drfailov/DRM_Watch_v2/Photos/2022-01-16 DRMW2_DOC.png

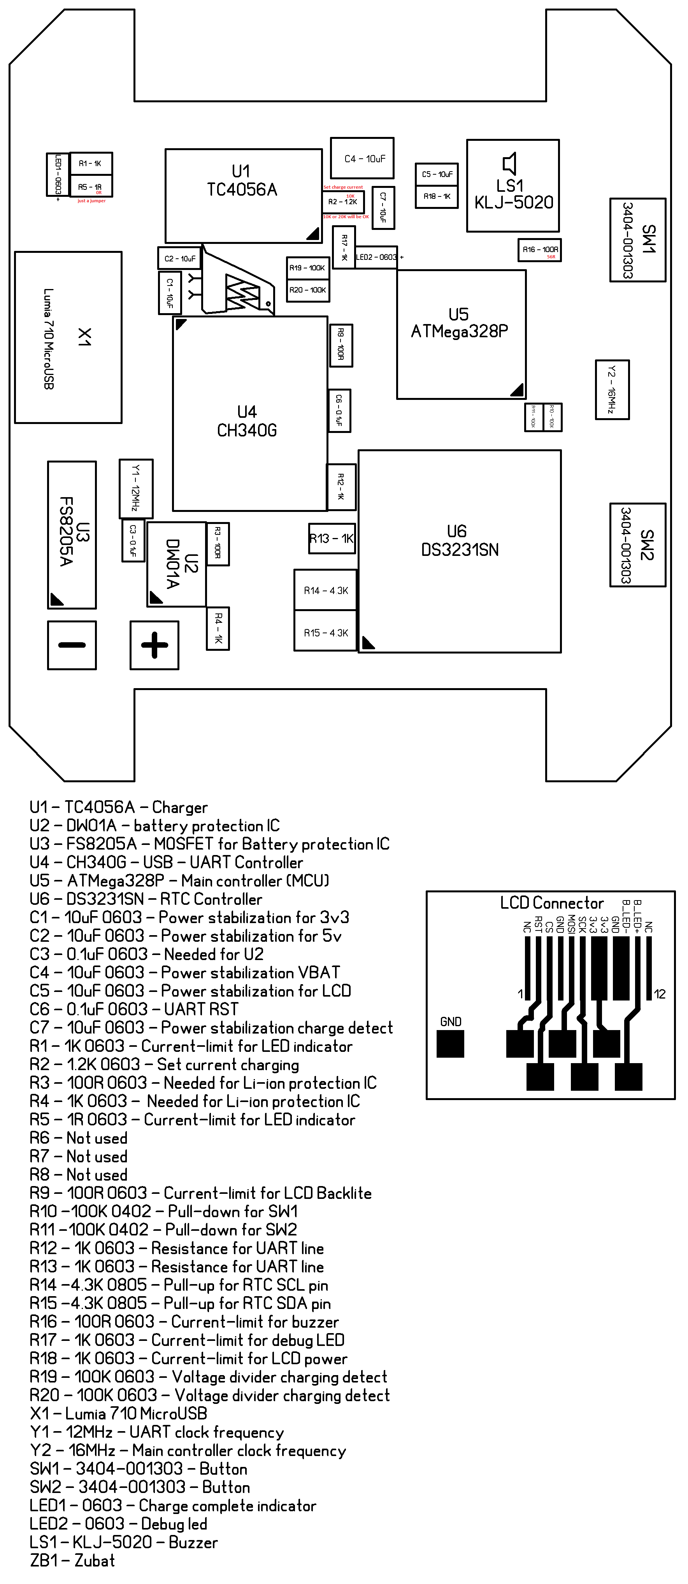
Photos/2022-01-16 DRMW2_DOC.png
