drfailov/DRM_Watch_v2/Photos/2022-03-02 Promo for repository DRM Watch.jpg

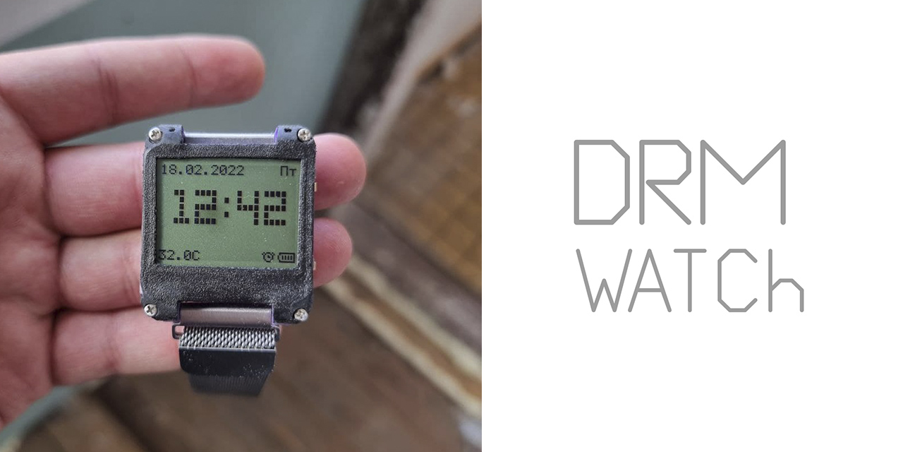
Photos/2022-03-02 Promo for repository DRM Watch.jpg
