drfailov/DRM_Watch_v2/Photos/20220228_160352.jpg

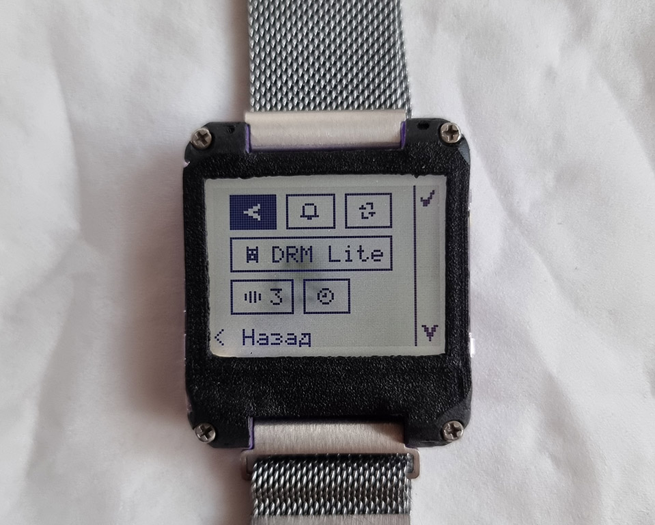
Photos/20220228_160352.jpg
