drfailov/DRM_Watch_v2/Photos/config_watchfaces.jpg

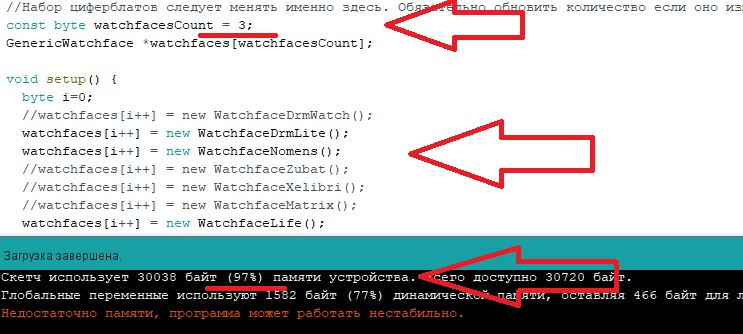
Photos/config_watchfaces.jpg
