drfailov/DRM_Watch_v2/Photos/DRMWatch.png

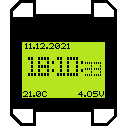
Photos/DRMWatch.png
