drfailov/DRM_Watch_v2/Photos/photo_2021-10-14_18-44-58.jpg

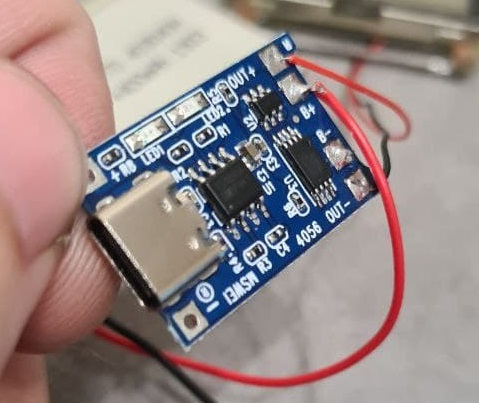
Photos/photo_2021-10-14_18-44-58.jpg
