drfailov/DRM_Watch_v2/Photos/photo_2021-10-16_11-53-57.jpg

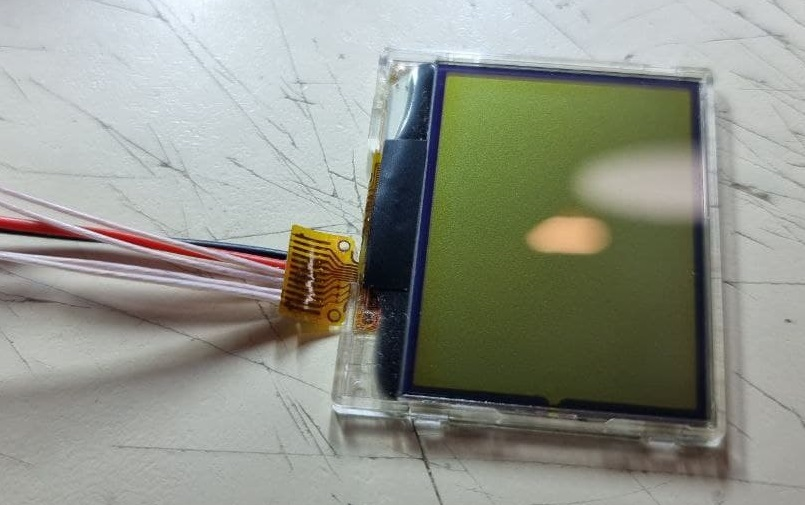
Photos/photo_2021-10-16_11-53-57.jpg
