drfailov/DRM_Watch_v2/Photos/photo_2021-11-30_09-08-52.jpg

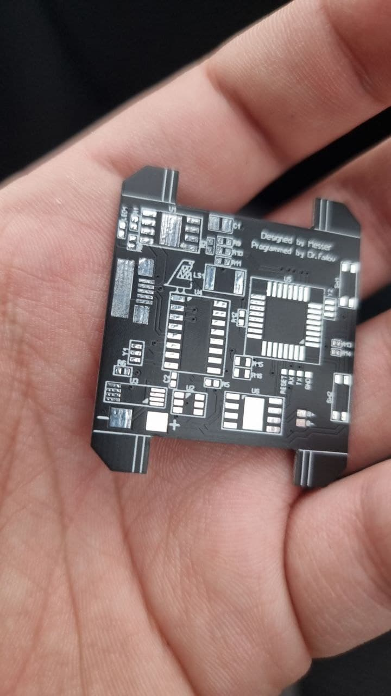
Photos/photo_2021-11-30_09-08-52.jpg
