drfailov/DRM_Watch_v2/Photos/photo_2021-12-01_08-44-34.jpg

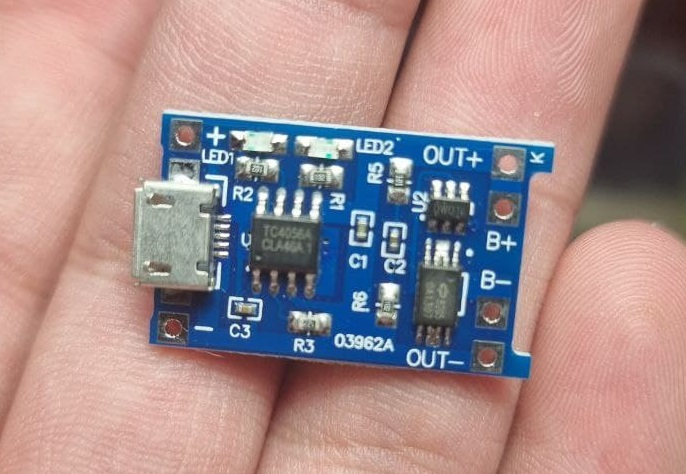
Photos/photo_2021-12-01_08-44-34.jpg
