drfailov/DRM_Watch_v2/Photos/photo_2021-12-01_15-29-12.jpg

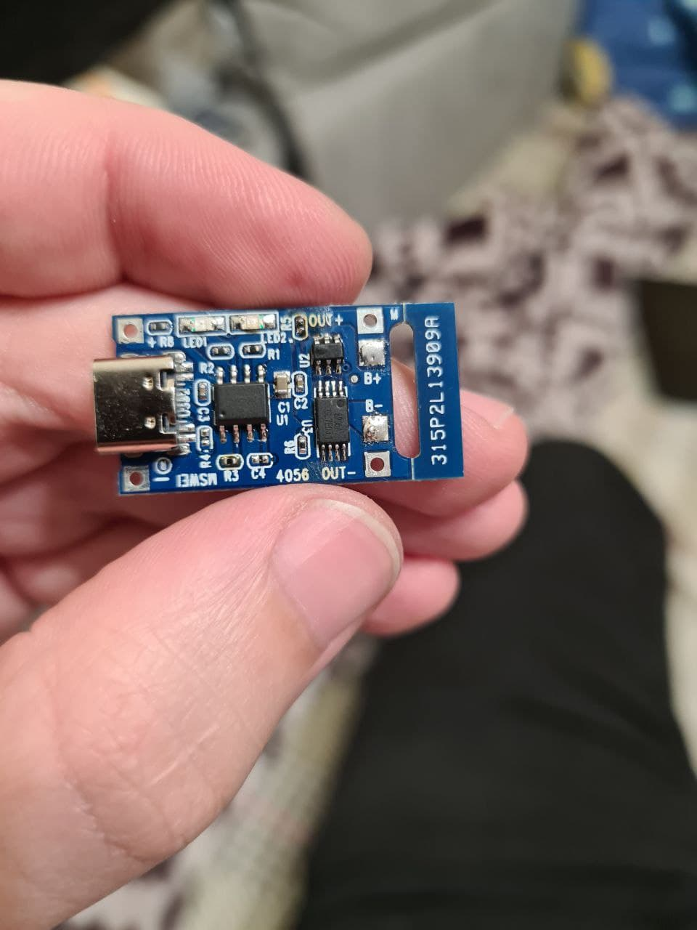
Photos/photo_2021-12-01_15-29-12.jpg
