drfailov/DRM_Watch_v2/Photos/photo_2021-12-19_19-43-52 (4).jpg

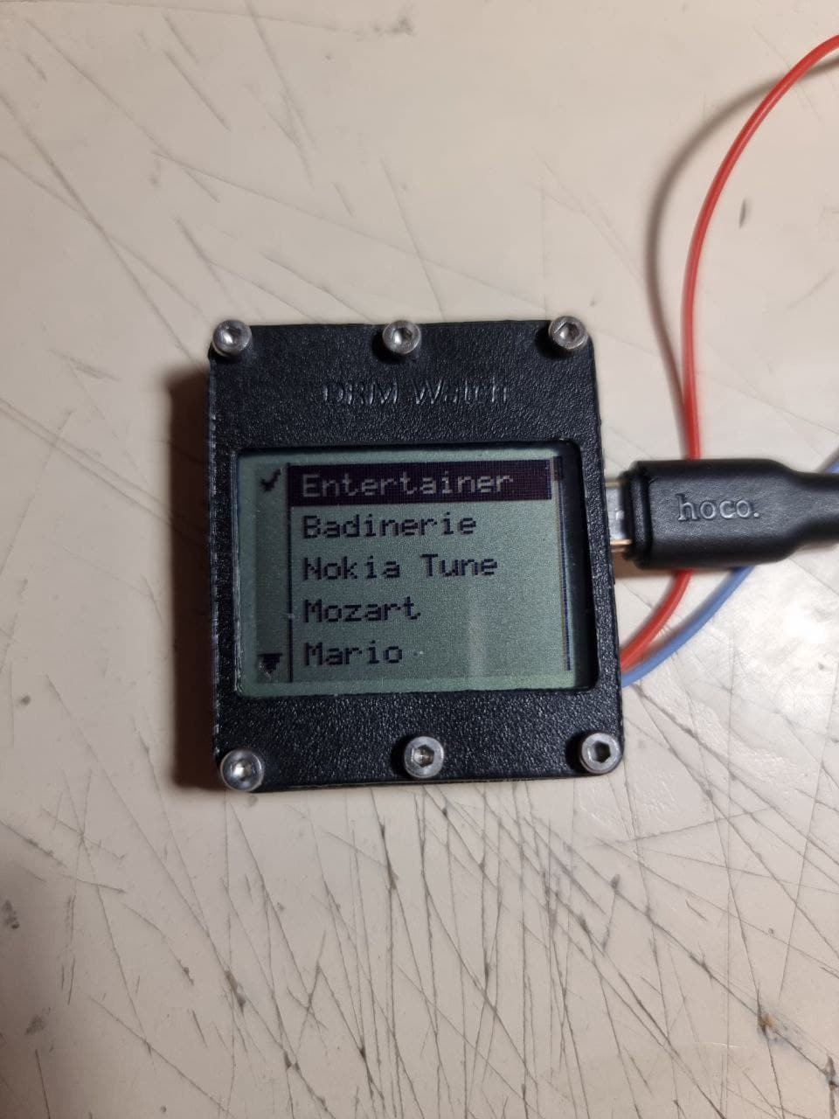
Photos/photo_2021-12-19_19-43-52 (4).jpg
