drfailov/DRM_Watch_v2/Photos/photo_2021-12-31_22-29-40.jpg

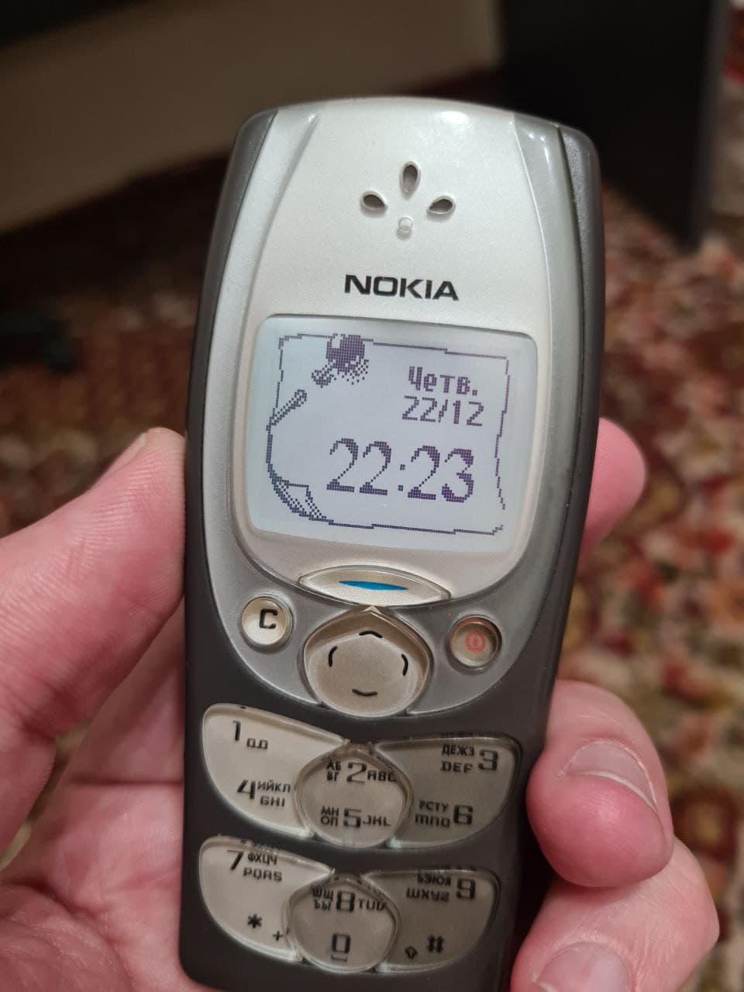
Photos/photo_2021-12-31_22-29-40.jpg
