drfailov/DRM_Watch_v2/Photos/photo_2022-01-07_13-40-24.jpg

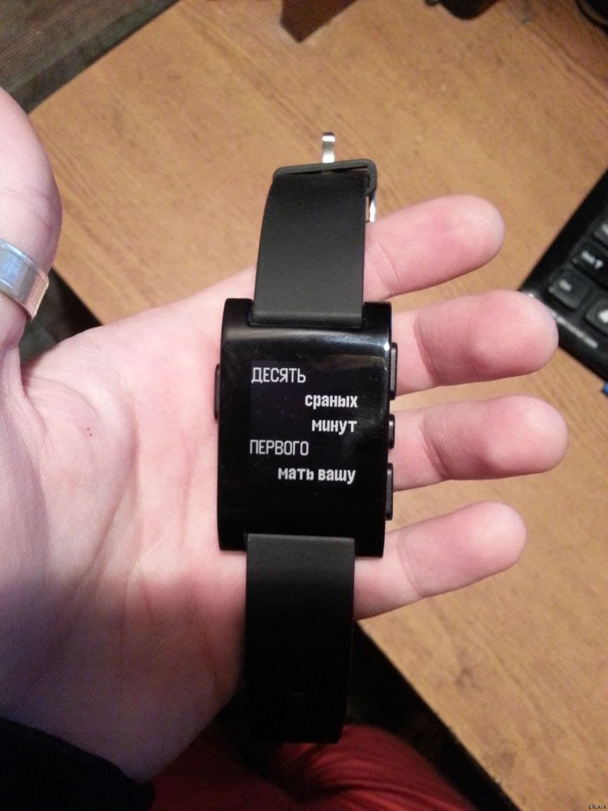
Photos/photo_2022-01-07_13-40-24.jpg
