drfailov/DRM_Watch_v2/Photos/photo_2022-03-16_15-22-59.jpg

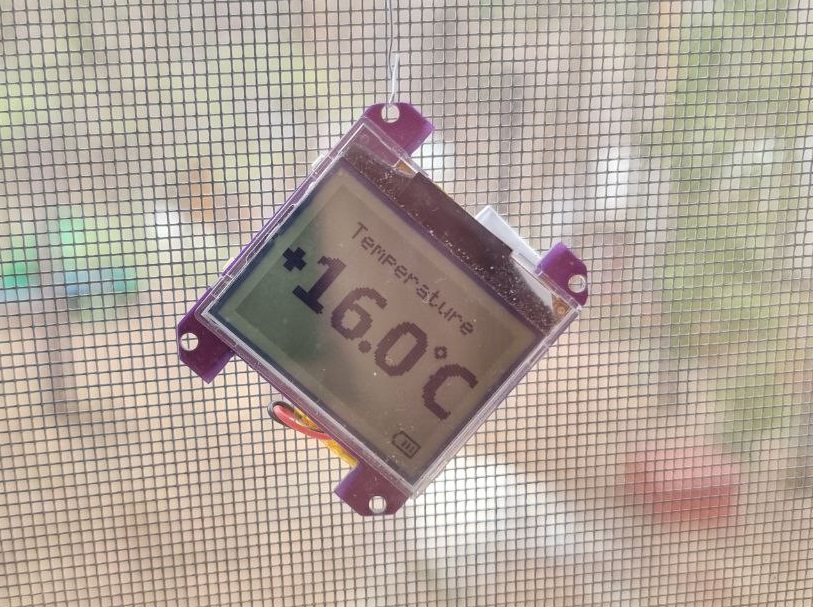
Photos/photo_2022-03-16_15-22-59.jpg
