drfailov/DRM_Watch_v2/Photos/photo_2023-04-07_19-43-56.jpg

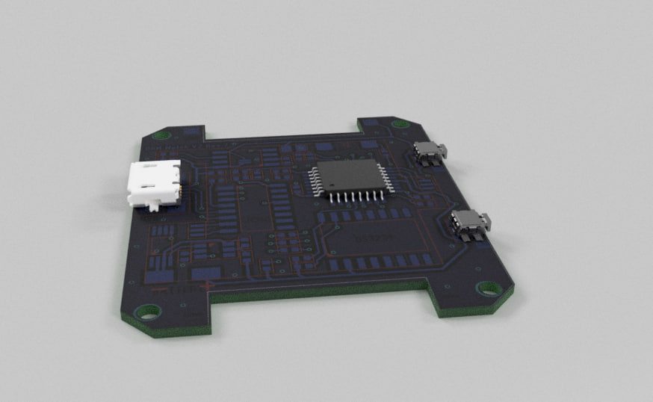
Photos/photo_2023-04-07_19-43-56.jpg
