drfailov/DRM_Watch_v2/Photos/photo_2023-04-19_00-23-33.jpg

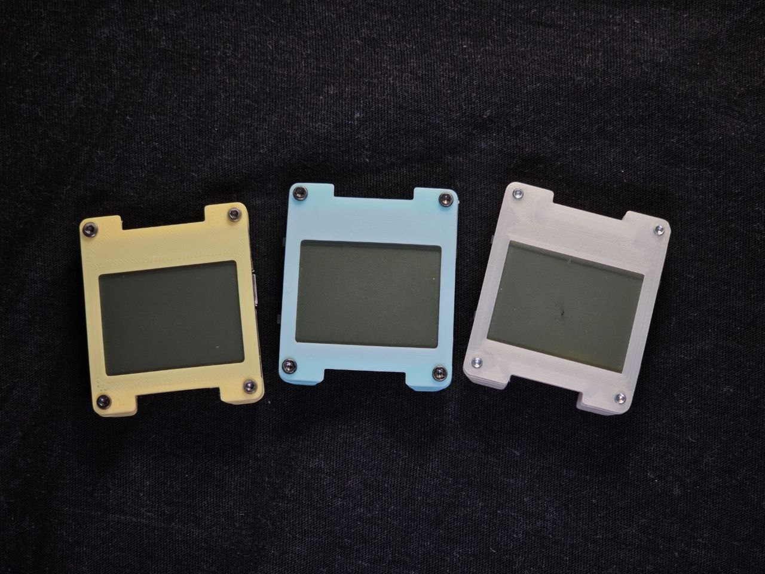
Photos/photo_2023-04-19_00-23-33.jpg
