drfailov/DRM_Watch_v2/Photos/Screenshot 2023-04-07 202631.jpg

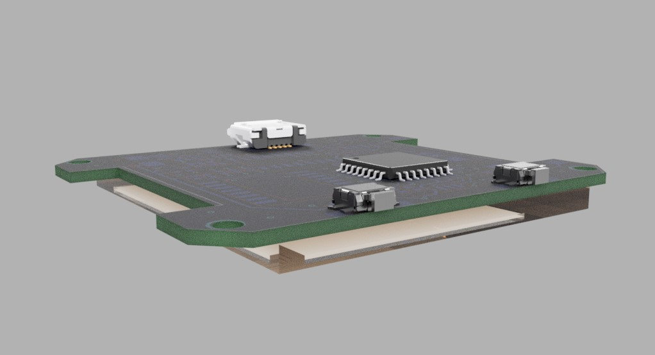
Photos/Screenshot 2023-04-07 202631.jpg
