drfailov/DRM_Watch_v2/Photos/Screenshot 2023-04-07 212515.jpg

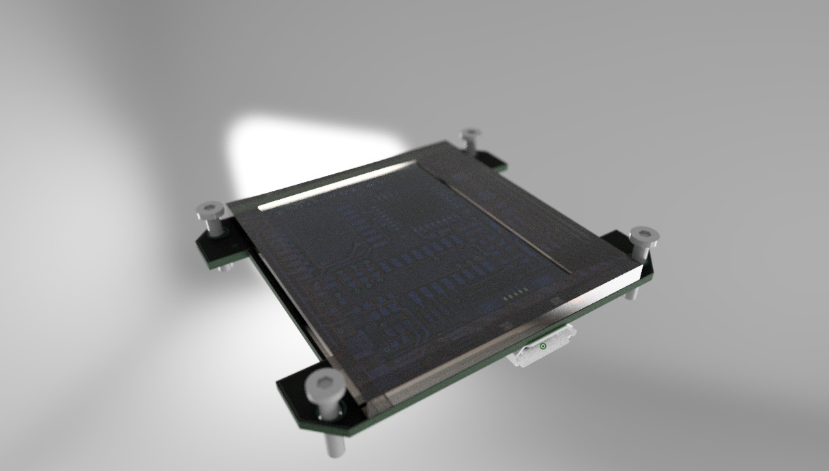
Photos/Screenshot 2023-04-07 212515.jpg
