drfailov/DRM_Watch_v2/Photos/Screenshot 2023-04-07 212542.jpg

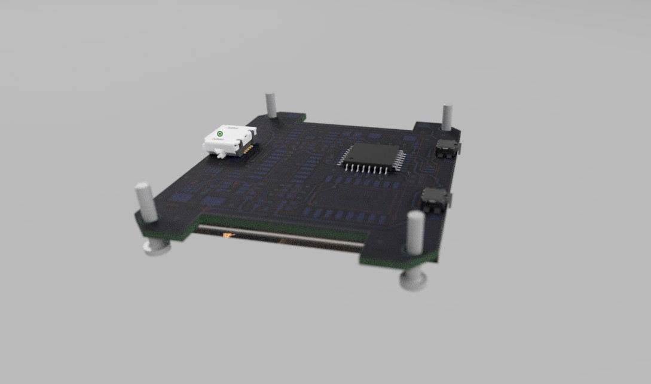
Photos/Screenshot 2023-04-07 212542.jpg
