drfailov/DRM_Watch_v2/Photos/v4 20mm.JPG

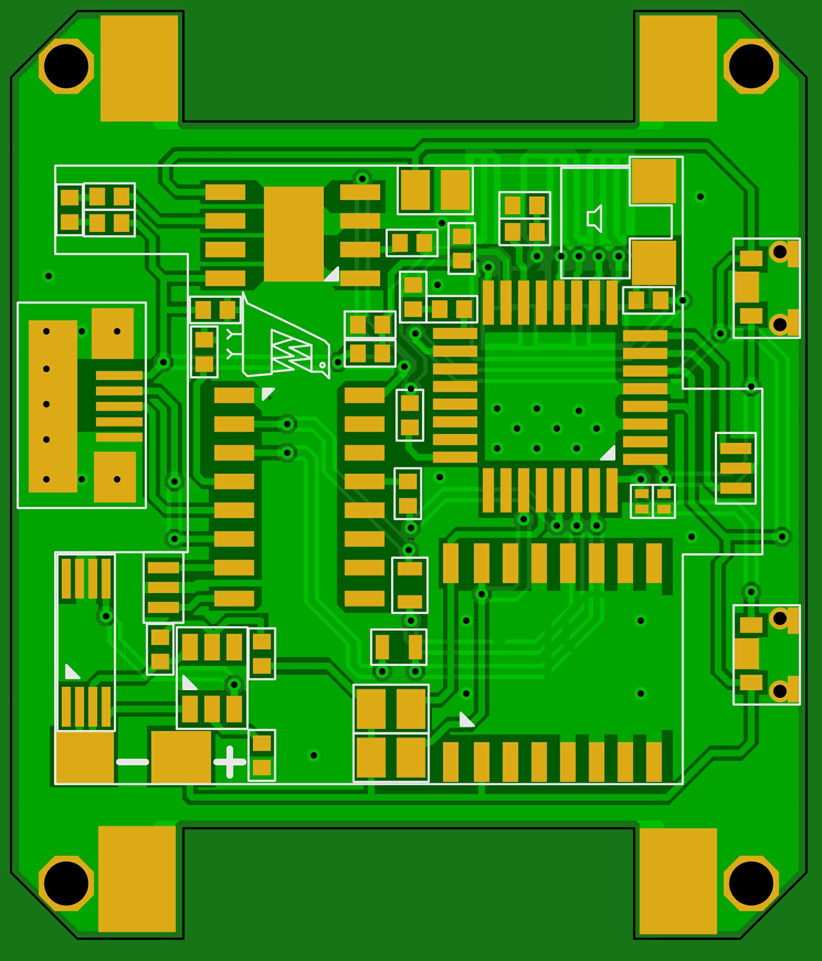
Photos/v4 20mm.JPG
