drfailov/DRM_Watch_v2/Case/Back Case v8.step

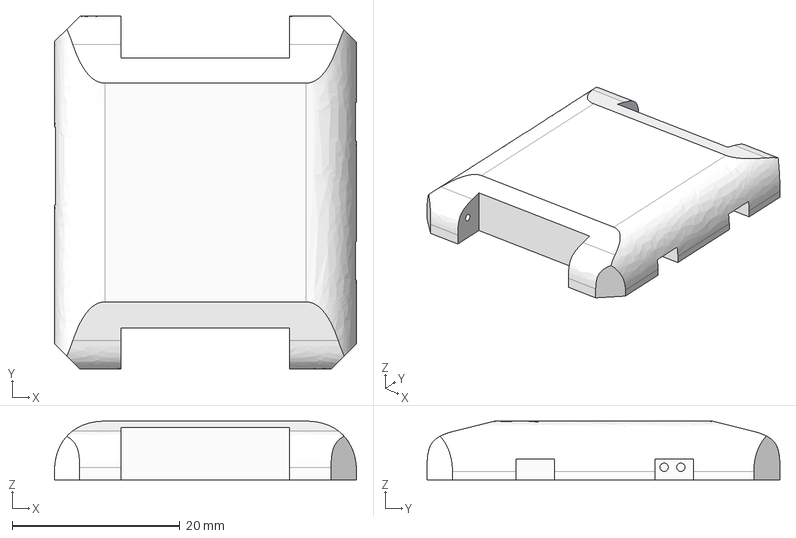
[picture p144: CAD file, 2022-01-25]
Case/Back Case v8.step
36.0 x 42.1 x 7.00 mm
