drfailov/DRM_Watch_v2/Arduino Program/_DRMWatch2/MelodyPlayer.ino

const byte groovyBlue[] PROGMEM = {
  125,
  0b10011101, 0b00100100, 0b00100100, 0b00100100, 0b00100100,
  0b10011000, 0b10011011, 0b10011000, 0b10011011, 0b10011101,
  0b00100100, 0b00100100, 0b00100100, 0b00100100, 0b10011000,
  0b10011011, 0b10011000, 0b10011011, 0b01011101, 0b10010001,
  0b01100100, 0b10010001, 0b01100100, 0b10010001, 0b01100100,
  0b10010001, 0b01100100, 0b10010001, 0b01100100, 0b10010001,
  0b01100100, 0b10011000, 0b10011011, 0b10011000, 0b10011011,
  0b01011101, 0b10011101, 0b01100100, 0b10011101, 0b01100100,
  0b10011101, 0b01100100, 0b10011101, 0b01100100, 0b10011101,
  0b01100100, 0b10011101, 0b01100100, 0b10011000, 0b10011011,
  0b10011000, 0b10011011, 0b01011101, 0b10011101, 0b01100000,
  0b10011101, 0b01100010, 0b10011101, 0b01100100, 0b10011101,
  0b01100000, 0b10011101, 0b10100010, 0b10100100, 0b10011101,
  0b01100100, 0b10011000, 0b10011011, 0b10011000, 0b10011011,
  0b01011101, 0b10011101, 0b01100000, 0b10011101, 0b01100010,
  0b10011101, 0b01100100, 0b10011101, 0b01100000, 0b10011101,
  0b10100010, 0b10100100, 0b10011101, 0b01100100, 0b10011000,
  0b10011011, 0b10011000, 0b10011011, 0b01011101, 0b10011101,
  0b01100000, 0b10011101, 0b01100011, 0b10011101, 0b01100010,
  0b10011101, 0b01100001, 0b10011101, 0b01100000, 0b10011101,
  0b01011111, 0b00100100, 0b10011000, 0b10011011, 0b10011000,
  0b10011011, 0b01011101, 0b11111111,
};
const byte* const getMelodyGroovyBlue() {
  return groovyBlue;
}


const byte blue[] PROGMEM = {
    140,
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

const char* const modeMenuMelodiesItems[] PROGMEM = {
  menuItemBack,
  modeMenuMelodiesItem1,
  modeMenuMelodiesItem2,
  modeMenuMelodiesItem3,
  modeMenuMelodiesItem4,
  modeMenuMelodiesItem5,
  modeMenuMelodiesItem6,
  modeMenuMelodiesItem7,
  modeMenuMelodiesItem8,
  modeMenuMelodiesItem9
};

byte getMelodyCount(){ return 9;}
const char* getMelodyName(byte index){
  return pgm_read_word(&modeMenuMelodiesItems[index+1]);
}
const byte* const getMelodyByIndex(byte index){
  if (index == 0) 
    return getMelodyEntertainer();
  if (index == 1)  
    return getMelodyBadinerie();
  if (index == 2)  
    return getMelodyNokiaTune();
  if (index == 3) 
    return getMelodyMozart();
  if (index == 4) 
    return getMelodyMario();
  if (index == 5) 
    return getMelodyGroovyBlue();
  if (index == 6) 
    return getMelodyUkraine();
  if (index == 7) 
    return getMelodyBlue();  
  if (index == 8) 
    return getMelodyWasWollenWirTrinken();    
}







bool melodyPlayerLoopMelody = false;

//return true if was played completely or false if interrupted
bool melodyPlayerPlayMelody(const byte* const melody) {
  displayTransition();
  melodyPlayerLoopMelody = false;
  do{
    melodyPlayerDrawScreen();
    pinMode(pinBuzzer, OUTPUT);
    byte length = melodyPlayerGetLength(melody);
    float tempo = pgm_read_byte(&melody[0]);
    float whole_notes_per_second = tempo / 240.0;
    for (byte i = 1; i < length - 1; i++) {
      byte b = pgm_read_byte(&melody[i]);
      byte duration = 0;
      if (bitRead(b, 7) == 0 && bitRead(b, 6) == 0) duration = 4;
      if (bitRead(b, 7) == 0 && bitRead(b, 6) == 1) duration = 8;
      if (bitRead(b, 7) == 1 && bitRead(b, 6) == 0) duration = 16;
      if (bitRead(b, 7) == 1 && bitRead(b, 6) == 1) duration = 32;
      float timeMs = 1000.0 / (whole_notes_per_second * duration);
      byte noteNumberByte = 0;
      for (byte i = 0; i < 6; i++)
        bitWrite(noteNumberByte, i, bitRead(b, i));
      float noteNumber = noteNumberByte;
      // Note frequency is calculated as (F*2^(n/12)),
      // We can use C2=65.41, or C3=130.81. C2 is a bit shorter.
      float frequency = 0;
      //290 is ok
      if (noteNumber < 36)
        frequency = 250.0 * pow(2.0, (noteNumber / 12.0));
  
      if (frequency != 0){
        displayBacklightOn();
        tone(pinBuzzer, frequency);
      }
      else{
        noTone(pinBuzzer);
      }
      long noteStarted = millis();
      while(millis() - noteStarted < timeMs);
      noTone(pinBuzzer);
      displayBacklightOff();
      delay(13);
      
      if (isButtonUpPressed()){
        if(isButtonUpHold()){
          melodyPlayerLoopMelody = !melodyPlayerLoopMelody;
          melodyPlayerDrawScreen();
        }
        else{
          displayBacklightOn();
          return false;
        }
      }
    }
    
    noTone(pinBuzzer);
    //pinMode(pinBuzzer, INPUT);
    delay(1000);
  }while(melodyPlayerLoopMelody);
  displayBacklightOn();
  return true;
}

void melodyPlayerDrawScreen() {
  displayClear();
  displayDrawVector(/*path*/getPathZubat(), /*x*/24, /*y*/10, /*animate*/false, /*color*/1);
#ifdef LANG_EN
  displayDrawText(20, 60, 1, F("Playing..."));
#endif
#ifdef LANG_RU
  displayDrawText(17, 60, 1, F("Пoпиликaeм!"));
#endif
#ifdef LANG_UA
  displayDrawText(20, 60, 1, F("Виконую..."));
#endif

  if(!melodyPlayerLoopMelody){
    byte hour = rtcGetHours();
    byte minute = rtcGetMinutes();
    sprintf(buffer, timeFormat, hour, minute);
    displayDrawText(0, 0, 1, buffer);
  }
  else{
    displayDrawIconFlip(0, 0, 1);
  }
  
  displayDrawBattery(79, 0);
  displayUpdate();
}

void printBits(byte myByte) {
  for (byte mask = 0x80; mask; mask >>= 1) {
    if (mask & myByte)
      Serial.print('1');
    else
      Serial.print('0');
  }
}

int melodyPlayerGetLength(const byte* const melody) {
  for (byte i = 0; i < 254; i++) {
    byte b = pgm_read_byte(&melody[i]);
    if (b == 0b11111111) {
      return i + 1;
    }
  }
}
