drfailov/DRM_Watch_v2/Arduino Program/_DRMWatch2/WatchfaceThermo.ino

// 'calibri0', 17x23px
const unsigned char  thermo0 [] PROGMEM = {
  0x80, 0xf0, 0xfc, 0xfe, 0xfe, 0x3f, 0x0f, 0x0f, 0x0f, 0x0f, 0x0f, 0x1f, 0xff, 0xfe, 0xfc, 0xf8, 
  0xe0, 0xff, 0xff, 0xff, 0xff, 0xff, 0x00, 0x00, 0x00, 0x00, 0x00, 0x00, 0x00, 0xff, 0xff, 0xff, 
  0xff, 0xff, 0x01, 0x0f, 0x1f, 0x3f, 0x7f, 0x7e, 0x78, 0x70, 0x70, 0x70, 0x78, 0x7c, 0x7f, 0x3f, 
  0x1f, 0x0f, 0x01
};
// 'calibri1', 17x23px
const unsigned char  thermo1 [] PROGMEM = {
  0x00, 0x00, 0x78, 0x38, 0x3c, 0x1c, 0x1e, 0xff, 0xff, 0xff, 0xff, 0xff, 0x00, 0x00, 0x00, 0x00, 
  0x00, 0x00, 0x00, 0x00, 0x00, 0x00, 0x00, 0x00, 0xff, 0xff, 0xff, 0xff, 0xff, 0x00, 0x00, 0x00, 
  0x00, 0x00, 0x00, 0x00, 0x78, 0x78, 0x78, 0x78, 0x78, 0x7f, 0x7f, 0x7f, 0x7f, 0x7f, 0x78, 0x78, 
  0x78, 0x78, 0x20
};
// 'calibri2', 17x23px
const unsigned char  thermo2 [] PROGMEM = {
  0x00, 0x3c, 0x1e, 0x1e, 0x0f, 0x0f, 0x0f, 0x0f, 0x0f, 0x1f, 0xff, 0xff, 0xfe, 0xfe, 0xfc, 0xf0, 
  0x00, 0x00, 0x00, 0x00, 0x00, 0x80, 0xc0, 0xe0, 0xf0, 0xf8, 0xfe, 0x7f, 0x3f, 0x1f, 0x0f, 0x07, 
  0x00, 0x00, 0x00, 0x7c, 0x7e, 0x7f, 0x7f, 0x7f, 0x7f, 0x7b, 0x79, 0x78, 0x78, 0x78, 0x78, 0x78, 
  0x78, 0x78, 0x70
};
// 'calibri3', 17x23px
const unsigned char  thermo3 [] PROGMEM = {
  0x00, 0x1c, 0x1e, 0x0e, 0x0f, 0x0f, 0x0f, 0x0f, 0x0f, 0x0f, 0xff, 0xff, 0xfe, 0xfe, 0xfc, 0x20, 
  0x00, 0x00, 0x00, 0x00, 0x1c, 0x1c, 0x1c, 0x1c, 0x1e, 0x1e, 0x3f, 0x7f, 0xff, 0xff, 0xf3, 0xf1, 
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
      byte temp3 = tempInt - (temp1 * 100) - (temp2 * 10); //265-(2*100)-(6*10)=5
      byte screenWidth = 96;
      byte textWidth = 96;
      if(!minus){
        textWidth = 86;
        if(temp < 10){
          textWidth = 67;
        }
      }
      int xPosition = (textWidth-screenWidth) / 2;

      if(minus)
        displayFillRect(/*x*/xPosition+0, /*y*/34, /*w*/10, /*h*/4, /*c*/1);
      if(temp1 != 0)
        drawNumber(/*x*/xPosition+10, /*y*/24, /*num*/temp1, /*animate*/ animate);
      drawNumberThermo(/*x*/xPosition+29, /*y*/24, /*num*/temp2, /*animate*/ animate);
      displayFillCircle(/*x*/xPosition+49, /*y*/44, /*r*/ 2, /*color*/ 1);
      drawNumberThermo(/*x*/xPosition+53, /*y*/24, /*num*/temp3, /*animate*/ animate);
      displayDrawBitmap(/*x*/xPosition+72, /*y*/23, /*bmp*/markC, /*w*/24, /*h*/24, /*COLOR*/1);
    }
    
    displayUpdate();
}



void drawNumberThermo(byte x, byte y, byte num, byte animate){
  if(num == 0)
    displayDrawBitmap(/*x*/x, /*y*/y, /*bmp*/thermo0, /*w*/17, /*h*/23, /*COLOR*/1);
  if(num == 1)
    displayDrawBitmap(/*x*/x, /*y*/y, /*bmp*/thermo1, /*w*/17, /*h*/23, /*COLOR*/1);
  if(num == 2)
    displayDrawBitmap(/*x*/x, /*y*/y, /*bmp*/thermo2, /*w*/17, /*h*/23, /*COLOR*/1);
  if(num == 3)
    displayDrawBitmap(/*x*/x, /*y*/y, /*bmp*/thermo3, /*w*/17, /*h*/23, /*COLOR*/1);
  if(num == 4)
    displayDrawBitmap(/*x*/x, /*y*/y, /*bmp*/thermo4, /*w*/17, /*h*/23, /*COLOR*/1);
  if(num == 5)
    displayDrawBitmap(/*x*/x, /*y*/y, /*bmp*/thermo5, /*w*/17, /*h*/23, /*COLOR*/1);
  if(num == 6)
    displayDrawBitmap(/*x*/x, /*y*/y, /*bmp*/thermo6, /*w*/17, /*h*/23, /*COLOR*/1);
  if(num == 7)
    displayDrawBitmap(/*x*/x, /*y*/y, /*bmp*/thermo7, /*w*/17, /*h*/23, /*COLOR*/1);
  if(num == 8)
    displayDrawBitmap(/*x*/x, /*y*/y, /*bmp*/thermo8, /*w*/17, /*h*/23, /*COLOR*/1);
  if(num == 9)
    displayDrawBitmap(/*x*/x, /*y*/y, /*bmp*/thermo9, /*w*/17, /*h*/23, /*COLOR*/1);
  if(animate)
    displayUpdate();
}
