drfailov/DRM_Watch_v2/Arduino Program/_DRMWatch2/WatchfaceXelibri.ino

void watchfaceXelibri(byte hour, byte minute, byte second, byte day, byte month, int year, byte dayOfWeek, byte animate)
{
  displayClear();

  {//battery
    displayDrawBattery(79, 61);
  }      
   
  {//date
    sprintf(buffer, "%2d ", day);
    if(month == 1)
      strcpy (buffer+3, "Jan");   
    if(month == 2)
      strcpy (buffer+3, "Feb");   
    if(month == 3)
      strcpy (buffer+3, "Mar");   
    if(month == 4)
      strcpy (buffer+3, "Apr");   
    if(month == 5)
      strcpy (buffer+3, "May");   
    if(month == 6)
      strcpy (buffer+3, "Jun");   
    if(month == 7)
      strcpy (buffer+3, "Jul");   
    if(month == 8)
      strcpy (buffer+3, "Aug");   
    if(month == 9)
      strcpy (buffer+3, "Sep");   
    if(month == 10)
      strcpy (buffer+3, "Oct");   
    if(month == 11)
      strcpy (buffer+3, "Now");   
    if(month == 12)
      strcpy (buffer+3, "Dec");   
    displayDrawText(29, 49, 1, buffer);
  }
  

  {//time
    byte hour1 = hour / 10;
    byte hour2 = hour - (hour1 * 10);
    byte minute1 = minute / 10;
    byte minute2 = minute - (minute1 * 10);
    drawNumberXelibri(/*x*/5, /*y*/12, /*num*/hour1, /*animate*/ animate);
    drawNumberXelibri(/*x*/26, /*y*/12, /*num*/hour2, /*animate*/ animate);
    displayDrawNumber(10, 47, 15, 4, 5, animate); // :
    drawNumberXelibri(/*x*/53, /*y*/12, /*num*/minute1, /*animate*/ animate);
    drawNumberXelibri(/*x*/74, /*y*/12, /*num*/minute2, /*animate*/ animate);
  }
  
}





//(Total bytes used to store images in PROGMEM = 1056)
// 'Xelibri0', 18x29px
const unsigned char bitmap_Xelibri0 [] PROGMEM = {
  0xe0, 0xf0, 0x00, 0xf8, 0xfa, 0x1b, 0x1b, 0x1b, 0x1b, 0x1b, 0x1b, 0x1b, 0x1b, 0xfa, 0xf8, 0x00, 
  0xf0, 0xe0, 0x0f, 0x1f, 0x00, 0xbf, 0xbf, 0x00, 0x00, 0x00, 0x00, 0x00, 0x00, 0x00, 0x00, 0xbf, 
  0xbf, 0x00, 0x1f, 0x0f, 0xfe, 0xff, 0x00, 0xff, 0xff, 0x00, 0x00, 0x00, 0x00, 0x00, 0x00, 0x00, 
  0x00, 0xff, 0xff, 0x00, 0xff, 0xfe, 0x00, 0x01, 0x00, 0x03, 0x0b, 0x1b, 0x1b, 0x1b, 0x1b, 0x1b, 
  0x1b, 0x1b, 0x1b, 0x0b, 0x03, 0x00, 0x01, 0x00
};
// 'Xelibri1', 8x29px
const unsigned char bitmap_Xelibri1 [] PROGMEM = {
  0x10, 0x18, 0x1a, 0xfb, 0xfb, 0x03, 0xff, 0xff, 0x00, 0x00, 0x00, 0x1f, 0xbf, 0x00, 0xbf, 0x1f, 
  0x00, 0x00, 0x00, 0xff, 0xff, 0x00, 0xff, 0xff, 0x00, 0x00, 0x00, 0x1f, 0x1f, 0x00, 0x1f, 0x1f

};
// 'Xelibri2', 18x29px
const unsigned char bitmap_Xelibri2 [] PROGMEM = {
  0x10, 0x18, 0x1a, 0x1b, 0x1b, 0x1b, 0x1b, 0x1b, 0x1b, 0x1b, 0x1b, 0x1b, 0x1b, 0xfa, 0xf8, 0x00, 
  0xf0, 0xe0, 0x00, 0x00, 0x00, 0x80, 0xa0, 0xb0, 0xb0, 0xb0, 0xb0, 0xb0, 0xb0, 0xb0, 0xb0, 0xbf, 
  0x3f, 0x00, 0x1f, 0x0f, 0xfe, 0xff, 0x00, 0xff, 0xff, 0x01, 0x01, 0x01, 0x01, 0x01, 0x01, 0x01, 
  0x01, 0x00, 0x00, 0x00, 0x00, 0x00, 0x1f, 0x1f, 0x18, 0x1b, 0x1b, 0x1b, 0x1b, 0x1b, 0x1b, 0x1b, 
  0x1b, 0x1b, 0x1b, 0x1b, 0x1b, 0x1b, 0x00, 0x00
};
// 'Xelibri3', 18x29px
const unsigned char bitmap_Xelibri3 [] PROGMEM = {
  0x10, 0x18, 0x1a, 0x1b, 0x1b, 0x1b, 0x1b, 0x1b, 0x1b, 0x1b, 0x1b, 0x1b, 0x1b, 0xfa, 0xf8, 0x00, 
  0xf0, 0xe0, 0x00, 0x00, 0x00, 0x00, 0xb0, 0xb0, 0xb0, 0xb0, 0xb0, 0xb0, 0xb0, 0xb0, 0xb0, 0xbf, 
  0xbf, 0x00, 0x1f, 0x0f, 0x00, 0x00, 0x00, 0x00, 0x01, 0x01, 0x01, 0x01, 0x01, 0x01, 0x01, 0x01, 
  0x01, 0xff, 0xff, 0x00, 0xff, 0xfe, 0x00, 0x1b, 0x1b, 0x1b, 0x1b, 0x1b, 0x1b, 0x1b, 0x1b, 0x1b, 
  0x1b, 0x1b, 0x1b, 0x0b, 0x03, 0x00, 0x01, 0x00
};
// 'Xelibri4', 18x29px
const unsigned char bitmap_Xelibri4 [] PROGMEM = {
  0x00, 0x00, 0x00, 0x00, 0x00, 0x00, 0x00, 0x00, 0x00, 0x00, 0x00, 0xf0, 0xf8, 0x00, 0xfe, 0xff, 
  0x00, 0x00, 0xc0, 0xe0, 0x80, 0xb8, 0xbc, 0xb0, 0xb0, 0xb0, 0xb0, 0xb0, 0xb0, 0xbf, 0xbf, 0x00, 
  0xbf, 0xbf, 0xb0, 0x10, 0x01, 0x01, 0x01, 0x01, 0x01, 0x01, 0x01, 0x01, 0x01, 0x01, 0x01, 0xff, 
  0xff, 0x00, 0xff, 0xff, 0x01, 0x01, 0x00, 0x00, 0x00, 0x00, 0x00, 0x00, 0x00, 0x00, 0x00, 0x00, 
  0x00, 0x1f, 0x1f, 0x00, 0x1f, 0x1f, 0x00, 0x00
};
// 'Xelibri5', 18x29px
const unsigned char bitmap_Xelibri5 [] PROGMEM = {
  0xff, 0xff, 0x03, 0xfb, 0xfb, 0x1b, 0x1b, 0x1b, 0x1b, 0x1b, 0x1b, 0x1b, 0x1b, 0x1b, 0x1b, 0x0b, 
  0x03, 0x00, 0x0f, 0x1f, 0x00, 0x3f, 0xbf, 0xb0, 0xb0, 0xb0, 0xb0, 0xb0, 0xb0, 0xb0, 0xb0, 0xa0, 
  0x80, 0x00, 0x00, 0x00, 0x00, 0x00, 0x00, 0x00, 0x00, 0x01, 0x01, 0x01, 0x01, 0x01, 0x01, 0x01, 
  0x01, 0xff, 0xff, 0x00, 0xff, 0xfe, 0x00, 0x00, 0x1b, 0x1b, 0x1b, 0x1b, 0x1b, 0x1b, 0x1b, 0x1b, 
  0x1b, 0x1b, 0x1b, 0x0b, 0x03, 0x00, 0x01, 0x00
};
// 'Xelibri6', 18x29px
const unsigned char bitmap_Xelibri6 [] PROGMEM = {
  0xe0, 0xf0, 0x00, 0xf8, 0xfa, 0x1b, 0x1b, 0x1b, 0x1b, 0x1b, 0x1b, 0x1b, 0x1b, 0x1b, 0x0b, 0x03, 
  0x01, 0x00, 0x0f, 0x1f, 0x00, 0xbf, 0xbf, 0xb0, 0xb0, 0xb0, 0xb0, 0xb0, 0xb0, 0xb0, 0xb0, 0xa0, 
  0x80, 0x00, 0x00, 0x00, 0xfe, 0xff, 0x00, 0xff, 0xff, 0x01, 0x01, 0x01, 0x01, 0x01, 0x01, 0x01, 
  0x01, 0xff, 0xff, 0x00, 0xff, 0xfe, 0x00, 0x01, 0x00, 0x03, 0x0b, 0x1b, 0x1b, 0x1b, 0x1b, 0x1b, 
  0x1b, 0x1b, 0x1b, 0x0b, 0x03, 0x00, 0x01, 0x00
};
// 'Xelibri7', 18x29px
const unsigned char bitmap_Xelibri7 [] PROGMEM = {
  0x10, 0x18, 0x1a, 0x1b, 0x1b, 0x1b, 0x1b, 0x1b, 0x1b, 0x1b, 0x1b, 0x1b, 0x1b, 0xfb, 0xfb, 0x03, 
  0xff, 0xff, 0x00, 0x00, 0x00, 0x00, 0x00, 0x00, 0x00, 0x80, 0xa0, 0xb0, 0x30, 0x30, 0x10, 0x0f, 
  0x07, 0x00, 0x01, 0x00, 0x00, 0x00, 0x00, 0x00, 0xfe, 0xff, 0x00, 0xff, 0xff, 0x00, 0x00, 0x00, 
  0x00, 0x00, 0x00, 0x00, 0x00, 0x00, 0x00, 0x00, 0x00, 0x00, 0x1f, 0x1f, 0x00, 0x1f, 0x1f, 0x00, 
  0x00, 0x00, 0x00, 0x00, 0x00, 0x00, 0x00, 0x00
};
// 'Xelibri8', 18x29px
const unsigned char bitmap_Xelibri8 [] PROGMEM = {
  0xe0, 0xf0, 0x00, 0xf8, 0xfa, 0x1b, 0x1b, 0x1b, 0x1b, 0x1b, 0x1b, 0x1b, 0x1b, 0xfa, 0xf8, 0x00, 
  0xf0, 0xe0, 0x03, 0x07, 0x00, 0x1f, 0xbf, 0xb0, 0xb0, 0xb0, 0xb0, 0xb0, 0xb0, 0xb0, 0xb0, 0xbf, 
  0x1f, 0x00, 0x07, 0x03, 0xf8, 0xfc, 0x00, 0xff, 0xff, 0x01, 0x01, 0x01, 0x01, 0x01, 0x01, 0x01, 
  0x01, 0xff, 0xff, 0x00, 0xfc, 0xf8, 0x00, 0x01, 0x00, 0x03, 0x0b, 0x1b, 0x1b, 0x1b, 0x1b, 0x1b, 
  0x1b, 0x1b, 0x1b, 0x0b, 0x03, 0x00, 0x01, 0x00
};
// 'Xelibri9', 18x29px
const unsigned char bitmap_Xelibri9 [] PROGMEM = {
  0xe0, 0xf0, 0x00, 0xf8, 0xfa, 0x1b, 0x1b, 0x1b, 0x1b, 0x1b, 0x1b, 0x1b, 0x1b, 0xfa, 0xf8, 0x00, 
  0xf0, 0xe0, 0x0f, 0x1f, 0x00, 0x3f, 0xbf, 0xb0, 0xb0, 0xb0, 0xb0, 0xb0, 0xb0, 0xb0, 0xb0, 0xbf, 
  0x3f, 0x00, 0x1f, 0x0f, 0x00, 0x00, 0x00, 0x00, 0x00, 0x01, 0x01, 0x01, 0x01, 0x01, 0x01, 0x01, 
  0x01, 0xff, 0xff, 0x00, 0xfc, 0xf8, 0x00, 0x00, 0x00, 0x1b, 0x1b, 0x1b, 0x1b, 0x1b, 0x1b, 0x1b, 
  0x1b, 0x1b, 0x1b, 0x0b, 0x03, 0x00, 0x01, 0x00
};



void drawNumberXelibri(byte x, byte y, byte num, byte animate){
  if(num == 0)
    displayDrawBitmap(/*x*/x, /*y*/y, /*bmp*/bitmap_Xelibri0, /*w*/18, /*h*/29, /*COLOR*/1);
  if(num == 1)
    displayDrawBitmap(/*x*/x+5, /*y*/y, /*bmp*/bitmap_Xelibri1, /*w*/8, /*h*/29, /*COLOR*/1);
  if(num == 2)
    displayDrawBitmap(/*x*/x, /*y*/y, /*bmp*/bitmap_Xelibri2, /*w*/18, /*h*/29, /*COLOR*/1);
  if(num == 3)
    displayDrawBitmap(/*x*/x, /*y*/y, /*bmp*/bitmap_Xelibri3, /*w*/18, /*h*/29, /*COLOR*/1);
  if(num == 4)
    displayDrawBitmap(/*x*/x, /*y*/y, /*bmp*/bitmap_Xelibri4, /*w*/18, /*h*/29, /*COLOR*/1);
  if(num == 5)
    displayDrawBitmap(/*x*/x, /*y*/y, /*bmp*/bitmap_Xelibri5, /*w*/18, /*h*/29, /*COLOR*/1);
  if(num == 6)
    displayDrawBitmap(/*x*/x, /*y*/y, /*bmp*/bitmap_Xelibri6, /*w*/18, /*h*/29, /*COLOR*/1);
  if(num == 7)
    displayDrawBitmap(/*x*/x, /*y*/y, /*bmp*/bitmap_Xelibri7, /*w*/18, /*h*/29, /*COLOR*/1);
  if(num == 8)
    displayDrawBitmap(/*x*/x, /*y*/y, /*bmp*/bitmap_Xelibri8, /*w*/18, /*h*/29, /*COLOR*/1);
  if(num == 9)
    displayDrawBitmap(/*x*/x, /*y*/y, /*bmp*/bitmap_Xelibri9, /*w*/18, /*h*/29, /*COLOR*/1);
  if(animate)
    displayUpdate();
}
