drfailov/DRM_Watch_v2/Arduino Program/_DRMWatch2/Generic.h

/*Данные, которые требуется по всей программе*/

#ifndef GENERIC_H
#define GENERIC_H



//Базовые константы
#define version F("v1.10")   //Версию менять здесь
//#define LANG_EN  //Раскомментировать чтобы использовать английский язык меню
#define LANG_RU   //Раскомментировать чтобы использовать русский язык меню
#define LOG   //Закомментировать чтобы отключило логи

//Распиновка
#define pinButtonDown (byte)2 //active high
#define pinButtonUp (byte)3 //active high
#define pinLcdRst (byte)5
#define pinLcdCs (byte)6
#define pinLcdMosi (byte)7
#define pinUsbVoltage (byte)9    //for old boards rev.1
//#define pinUsbVoltage (byte)11  //for new boards  rev.2
#define pinLcdPower (byte)10
#define pinLcdSck (byte)11   //for old boards  rev.1
//#define pinLcdSck (byte)8    //for new boards  rev.2
#define pinBuzzer (byte)12 //passive
#define pinLed (byte)13  //active high
// A0 - Random seed sourde (leave unconnected)
#define pinLcdBacklight (byte)15  //A1, active high
// A4 - RTC SDA
// A5 - RTC SCL

//размер текстового буфера. Чем меньше тем экономнее.
#define BUFFER_SIZE 25

  
//Здесь определенл, которое используется во всех меню, для экономии памяти
#ifdef LANG_RU
const char menuItemBack[] PROGMEM = "< Haзaд";
const char textSaved[] PROGMEM = "Coxpaнeнo";
#endif
#ifdef LANG_EN
const char menuItemBack[] PROGMEM = "< Back";
const char textSaved[] PROGMEM = "Saved";
#endif

class Generic_{
  
  public:
  
  const char* getMenuItemBack(){ 
    return menuItemBack;
  }
  static const char* getTextSaved(){ 
    return menuItemBack;
  }

  
  //общий на всю программу текстовый буфер чтобы не объявлять каждый раз локальную.
  char buffer[BUFFER_SIZE]; 
  char* getDateFormat(){return "%02d.%02d.%04d";}
  

};

static Generic_ Generic;

#endif
