drfailov/DRM_Watch_v2/Arduino Program/_DRMWatch2/RTC.ino

/*Global RTC-related functions*/

#include <DS3231M.h>  // Include the DS3231M RTC library

DS3231M_Class DS3231M;  ///< Create an instance of the DS3231M class
  bool rtcReady = false;
  
  
  void rtcInit() {
  #ifdef LOG
    Serial.print(F("DS3231M..."));
  #endif
    Wire.setWireTimeout(3000, true); //timeout value in uSec - SBWire uses 100 uSec, so 1000 should be OK
    while (!DS3231M.begin())  // Initialize RTC communications
    {
  #ifdef LOG
      Serial.println(F("FAIL"));
  #endif
  #ifdef LANG_EN
      displayMessage(F("RTC FAIL"));
  #endif
  #ifdef LANG_RU
      displayMessage(F("Ошибка RTC"));
  #endif
  #ifdef LANG_RU
      displayMessage(F("Пoмилкa RTC"));
  #endif
      delay(300);
    }                         // of loop until device is located
    DS3231M.pinSquareWave();  // Make INT/SQW pin toggle at 1Hz
    rtcReady = true;
  #ifdef LOG
    Serial.print(F("OK,Temp="));
    Serial.println(DS3231M.temperature());
  #endif
  }
  
  void rtcSetTime(int year, byte month, byte day, byte hour, byte minute) {
    DS3231M.adjust(DateTime(year, month, day, hour, minute, 0));  // Adjust the RTC date/time
  }
  
  byte rtcGetSeconds() {
    DateTime now = DS3231M.now();
    return now.second();
  }
  
  byte rtcGetMinutes() {
    DateTime now = DS3231M.now();
    return now.minute();
  }
  
  byte rtcGetHours() {
    DateTime now = DS3231M.now();
    return now.hour();
  }
  
  byte rtcGetDay() {
    DateTime now = DS3231M.now();
    return now.day();
  }
  
  byte rtcGetDayOfWeek() {
    DateTime now = DS3231M.now();
    return now.dayOfTheWeek();
  }
  
  byte rtcGetMonth() {
    DateTime now = DS3231M.now();
    return now.month();
  }
  
  int rtcGetYear() {
    DateTime now = DS3231M.now();
    return now.year();
  }
  
  float rtcGetTemp() {
    float temp =  DS3231M.temperature() / 100.0;
    return temp;
  }
